rbroich/modair/design/diagrams/can_id_format_white.png

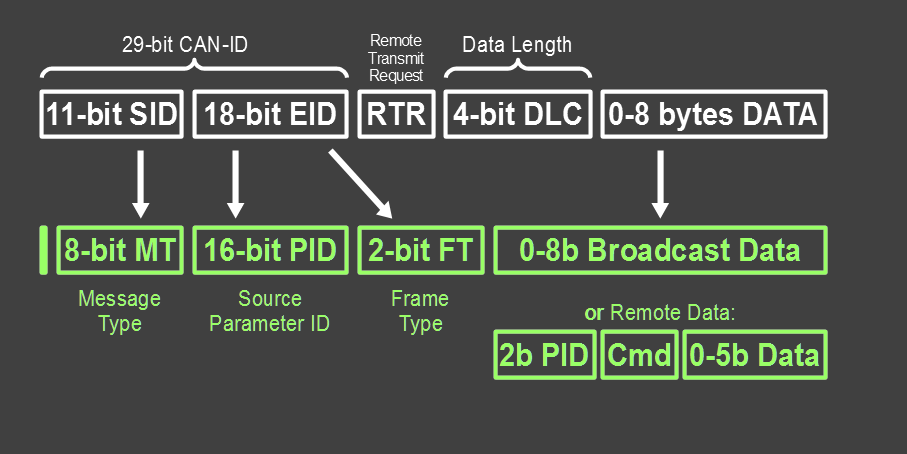
design/diagrams/can_id_format_white.png
