rbroich/modair/design/diagrams/module_overview_black.png

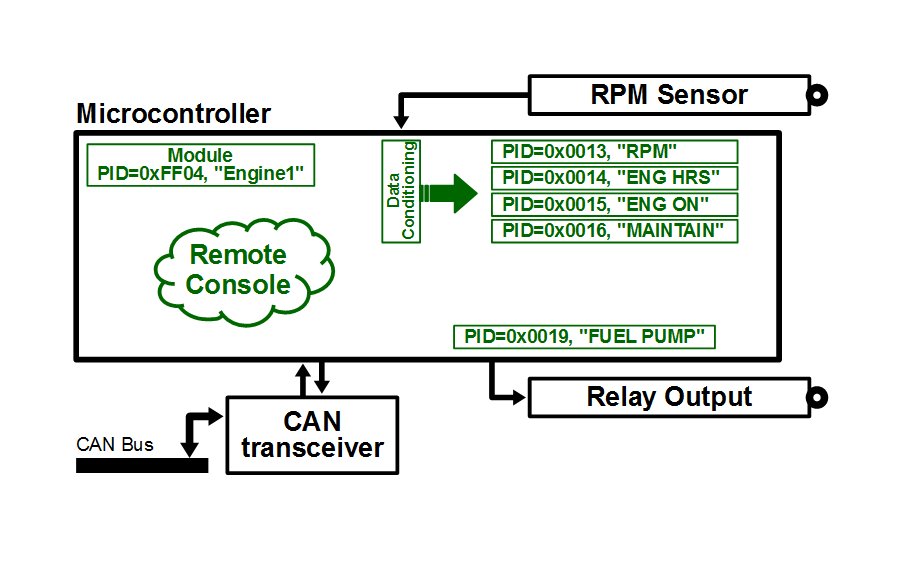
design/diagrams/module_overview_black.png
