rbroich/modair/design/diagrams/monochrome_lcd_module_black.png

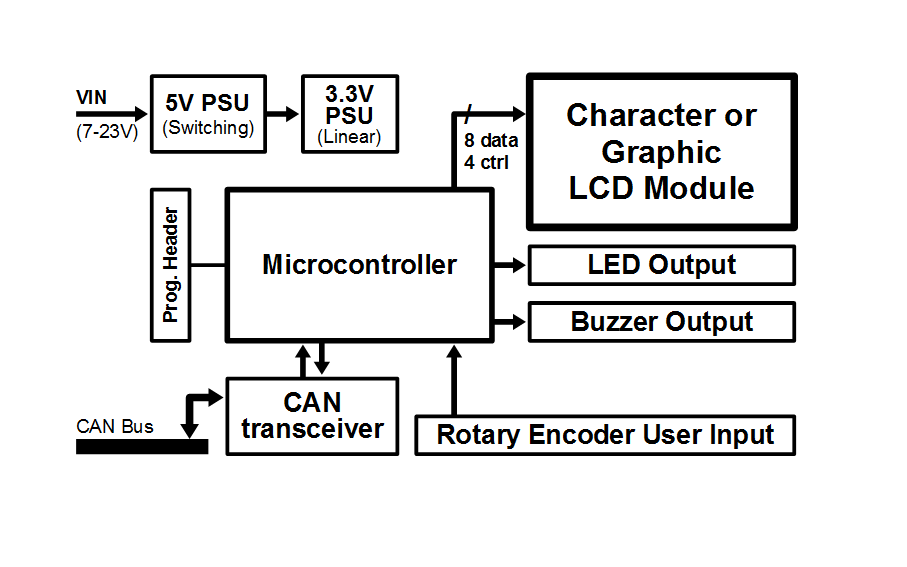
design/diagrams/monochrome_lcd_module_black.png
