rbroich/modair/design/diagrams/monochrome_lcd_module_white.png

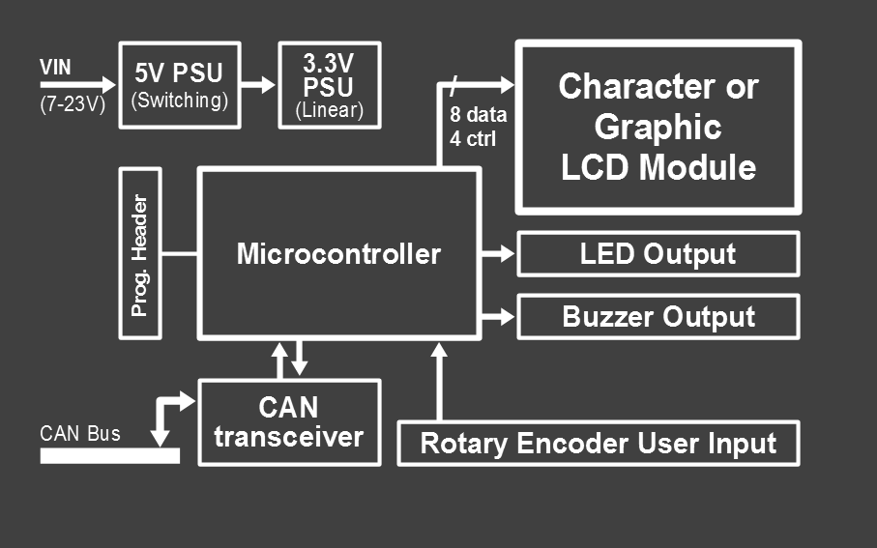
design/diagrams/monochrome_lcd_module_white.png
