rbroich/modair/design/diagrams/navigation_module_black.png

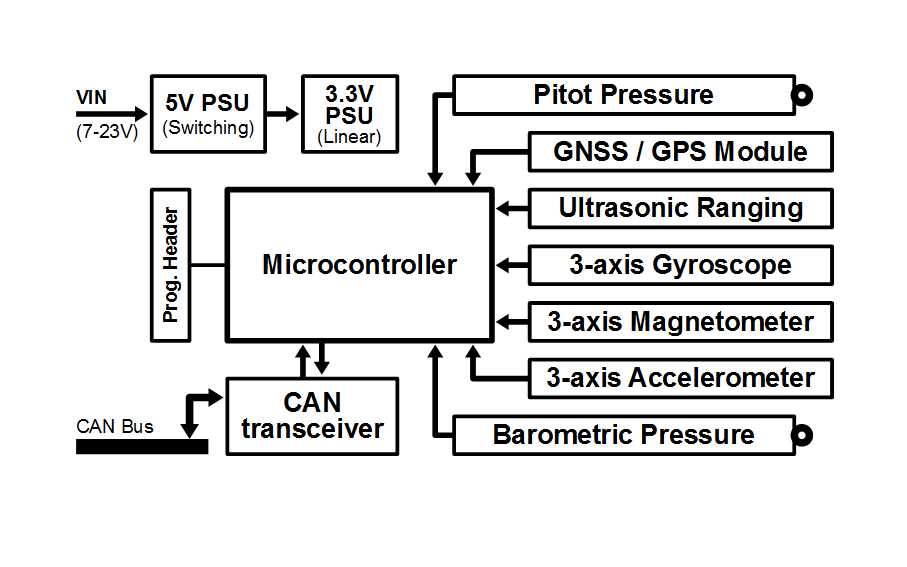
design/diagrams/navigation_module_black.png
