rbroich/modair/design/diagrams/remote_console_black.png

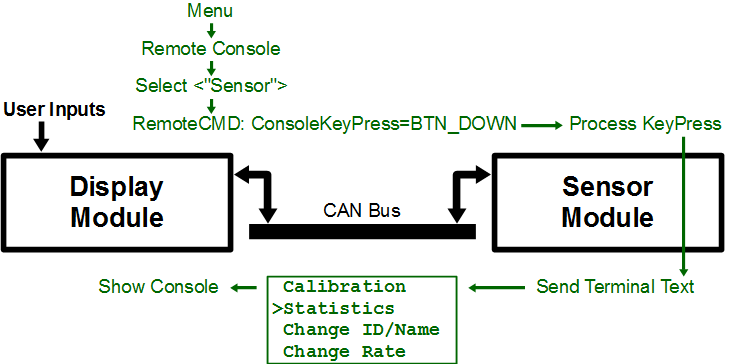
design/diagrams/remote_console_black.png
