rbroich/modair/design/diagrams/remote_console_white.png

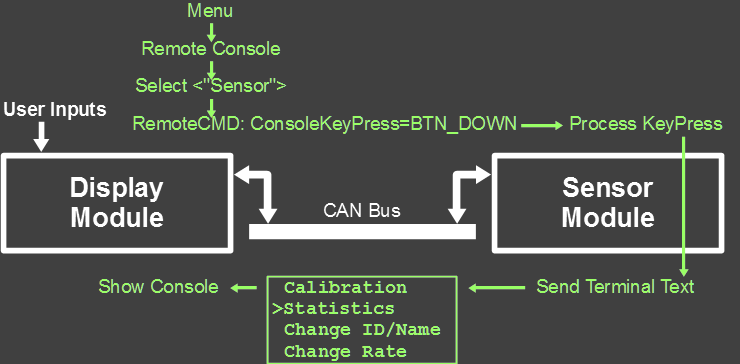
design/diagrams/remote_console_white.png
