rbroich/modair/design/diagrams/rotax_engine_module_white.png

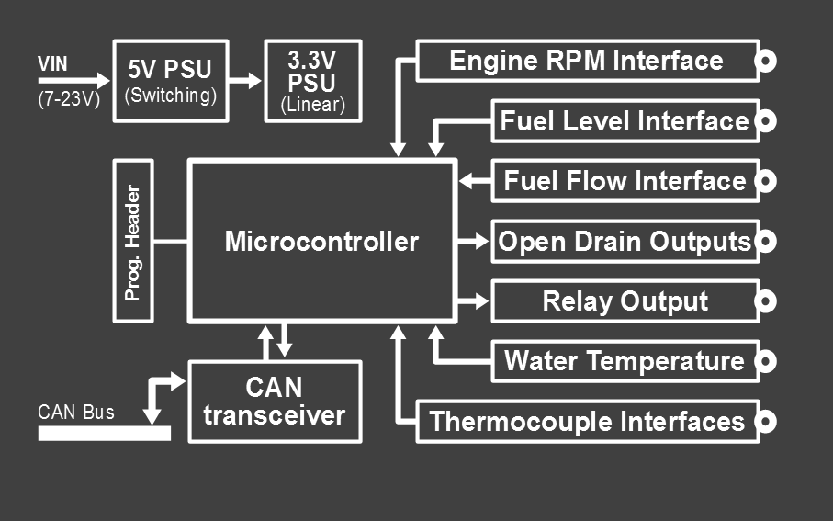
design/diagrams/rotax_engine_module_white.png
