rbroich/modair/design/diagrams/sensor_widgets_black.png

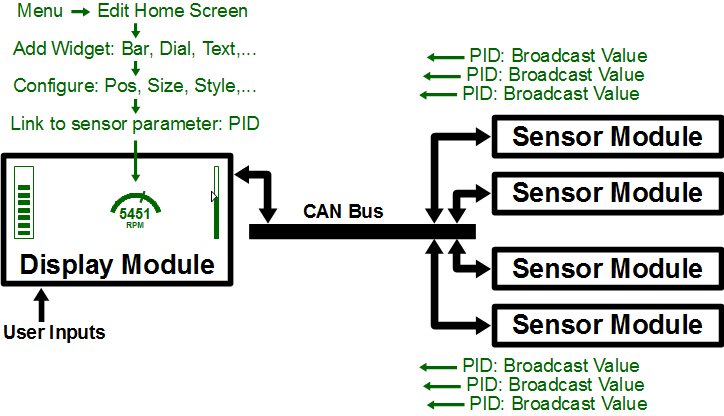
design/diagrams/sensor_widgets_black.png
