rbroich/modair/design/diagrams/sensor_widgets_white.png

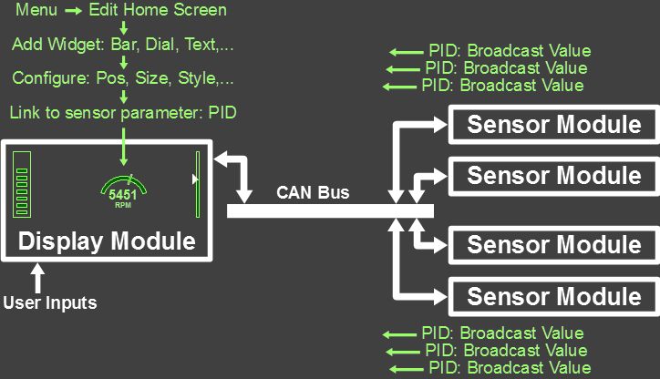
design/diagrams/sensor_widgets_white.png
