rbroich/modair/design/diagrams/simple_block_diagram_black.png

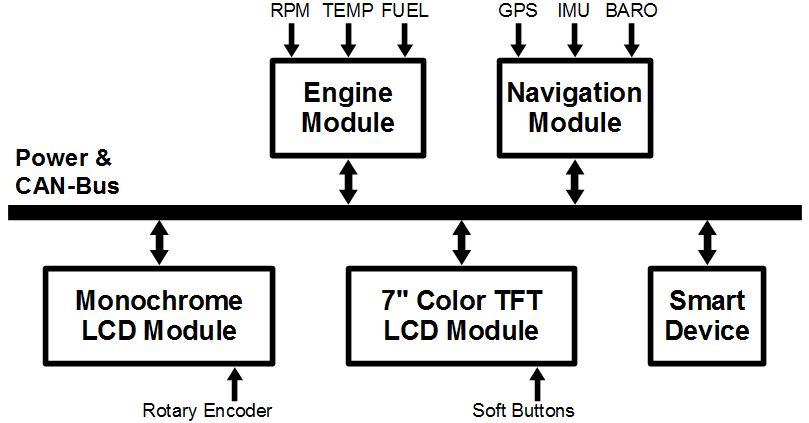
design/diagrams/simple_block_diagram_black.png
