rbroich/modair/modules/display_parallel/mechanical/solidworks_brackets/erm25664_bracket.JPG

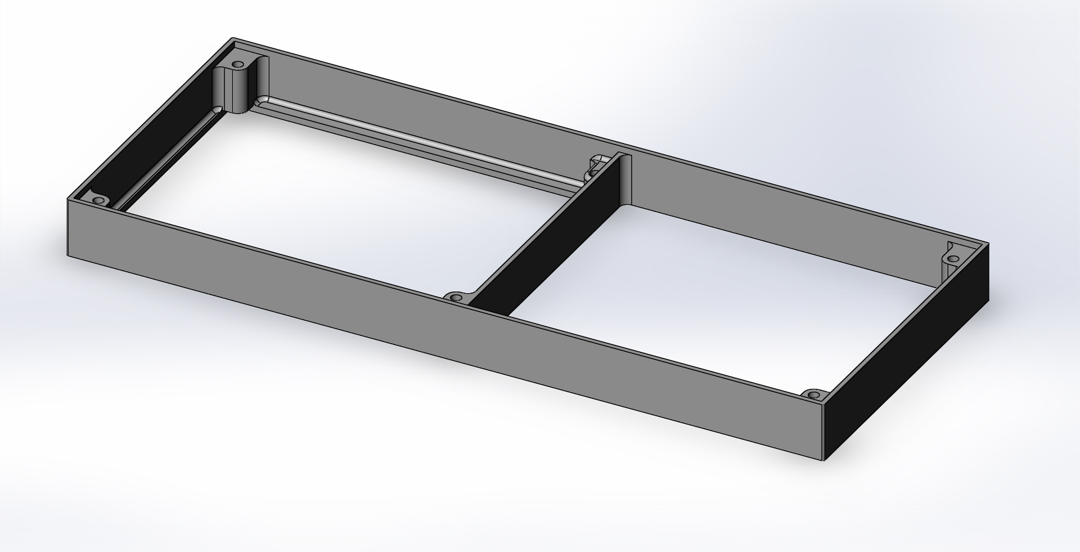
modules/display_parallel/mechanical/solidworks_brackets/erm25664_bracket.JPG
