rbroich/modair/modules/display_parallel/mechanical/solidworks_brackets/g12864b_bracket.JPG

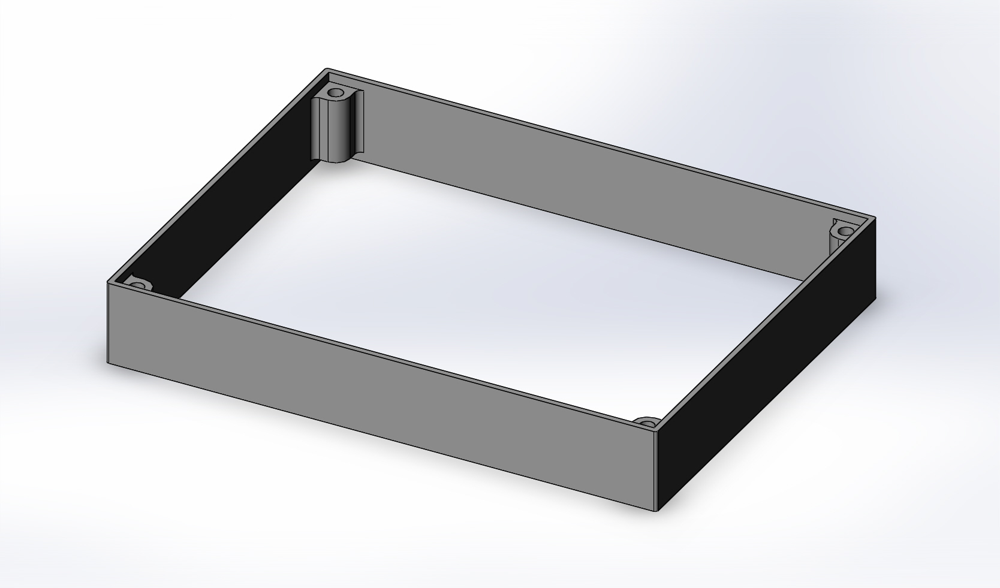
modules/display_parallel/mechanical/solidworks_brackets/g12864b_bracket.JPG
