rbroich/modair/modules/navigation/firmware/dspic_nav/module_console.h

#ifndef MODULE_CONSOLE_H
#define MODULE_CONSOLE_H

#include "common.h"

void* menu_fnc_homescreen(u8 zero, u8 key_input);
    void* menu_fnc_version(u8 zero, u8 key_input);
    void* menu_fnc_changesettings(u8 zero, u8 key_input);
        void* menu_fnc_changeid(u8 zero, u8 key_input);
        void* menu_fnc_changename(u8 zero, u8 key_input);
        void* menu_fnc_changerate(u8 zero, u8 key_input);

#endif
