rbroich/modair/modules/display_parallel/firmware/dspic_erm/ecan_mod.h

#ifndef ECAN_MOD_H
#define ECAN_MOD_H

#include "common.h"

#define NR_ECAN_BUF             16 // first 8 are Tx, last 8 are Rx

#define U1TXt                   TRISBbits.TRISB7
#define U1TX                    LATBbits.LATB7
#define U1RXa                   ANSELBbits.ANSB8
#define U1RXt                   TRISBbits.TRISB8
#define U1RX                    PORTBbits.RB8

#define ECAN_FLAGS_RTR          0x04

void ecan_irq(void);
void ecan_tx(u16 pid, u16 d0, u16 d2, u16 d4, u16 d6, u8 msg_type, u8 len, u8 flags);
// extern void ecan_rx(u16 pid, u16 *data, u8 msg_type, u8 flags, u8 len);
void ecan_init(void);

#endif
