rbroich/modair/modules/display_parallel/firmware/dspic_ntg128641a/glcd_font3x5.h

const unsigned char font3x5[] = {
    0x00, 0x00, 0x00, // (space)
    0x17, 0x00, 0x00, // !
    0x03, 0x00, 0x03, // "
    0x0A, 0x1F, 0x0A, // #
    0x16, 0x13, 0x1A, // 0x
    0x09, 0x04, 0x0A, // %
    0x0A, 0x15, 0x1A, // &
    0x03, 0x00, 0x00, // '
    0x00, 0x0E, 0x11, // (
    0x11, 0x0E, 0x00, // )
    0x06, 0x06, 0x00, // *
    0x04, 0x0E, 0x04, // +
    0x0C, 0x1C, 0x00, // ,
    0x04, 0x04, 0x04, // -
    0x10, 0x00, 0x00, // .
    0x18, 0x04, 0x03, // /
    0x1F, 0x11, 0x1F, // 0
    0x02, 0x1F, 0x00, // 1
    0x1D, 0x15, 0x17, // 2
    0x15, 0x15, 0x1F, // 3
    0x0F, 0x08, 0x1E, // 4
    0x17, 0x15, 0x1D, // 5
    0x1F, 0x15, 0x1D, // 6
    0x01, 0x01, 0x1F, // 7
    0x1F, 0x15, 0x1F, // 8
    0x17, 0x15, 0x1F, // 9
    0x00, 0x0A, 0x00, // :
    0x00, 0x1A, 0x00, // ;
    0x04, 0x0A, 0x11, // <
    0x0A, 0x0A, 0x0A, // =
    0x11, 0x0A, 0x04, // >
    0x00, 0x15, 0x07, // ?
    0x1F, 0x15, 0x17, // @
    0x1F, 0x05, 0x1F, // A
    0x1F, 0x15, 0x1B, // B
    0x1F, 0x11, 0x11, // C
    0x1F, 0x11, 0x0E, // D
    0x1F, 0x15, 0x15, // E
    0x1F, 0x05, 0x01, // F
    0x1F, 0x11, 0x1D, // G
    0x1F, 0x04, 0x1F, // H
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
    0x1F, 0x1F, 0x1F  // fill
};
