rbroich/modair/modules/display_parallel/firmware/dspic_ntg128641a/glcd_font4x5.h

const unsigned char font4x5[] = {
    0x00, 0x00, 0x00, // (space)
    0x00, 0x17, 0x00, // !
    0x03, 0x00, 0x03, // "
    0x1f, 0x0a, 0x1f, // #
    0x14, 0x1f, 0x0a, // $
    0x09, 0x04, 0x12, // %
    0x1a, 0x15, 0x1e, // &
    0x03, 0x01, 0x00, // '
    0x0e, 0x11, 0x00, // (
    0x11, 0x0e, 0x00, // )
    0x15, 0x0e, 0x15, //
    0x04, 0x0e, 0x04, // +
    0x10, 0x10, 0x00, // ,
    0x04, 0x04, 0x04, // -
    0x00, 0x10, 0x00, // .
    0x18, 0x04, 0x03, // /
    0x1e, 0x11, 0x0f, // 0
    0x12, 0x1f, 0x10, // 1
    0x19, 0x15, 0x12, // 2
    0x11, 0x15, 0x0a, // 3
    0x06, 0x04, 0x1f, // 4
    0x17, 0x15, 0x09, // 5
    0x0e, 0x15, 0x08, // 6
    0x01, 0x1d, 0x03, // 7
    0x0a, 0x15, 0x0a, // 8
    0x02, 0x15, 0x0e, // 9
    0x00, 0x14, 0x00, // :
    0x10, 0x14, 0x00, // ;
    0x04, 0x0a, 0x11, // <
    0x14, 0x14, 0x14, // =
    0x11, 0x0a, 0x04, // >
    0x01, 0x15, 0x02, // ?
    0x1f, 0x11, 0x17, // @
    0x1e, 0x05, 0x1e, // A
    0x1f, 0x15, 0x0a, // B
    0x0e, 0x11, 0x11, // C
    0x1f, 0x11, 0x0e, // D
    0x1f, 0x15, 0x11, // E
    0x1f, 0x05, 0x01, // F
    0x0e, 0x11, 0x1d, // G
    0x1f, 0x04, 0x1f, // H
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
};
